wangjingye342/agent-bell/agent_bell/astronaut_frames.h

// 自动生成（tools/gen_astronaut.py）：绕头脚中轴自转太空人，24 帧 48x48，U8g2 XBM 位序
#pragma once
#include <Arduino.h>
#define ASTRO_W 48
#define ASTRO_H 48
#define ASTRO_N 24
const uint8_t ASTRO[24][288] PROGMEM = {
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
};
